arbehbaha/3U_X-Band_CubeSat_Reflectarray_Thesis/Chamber_Code/Media/RA+Narda.jpg

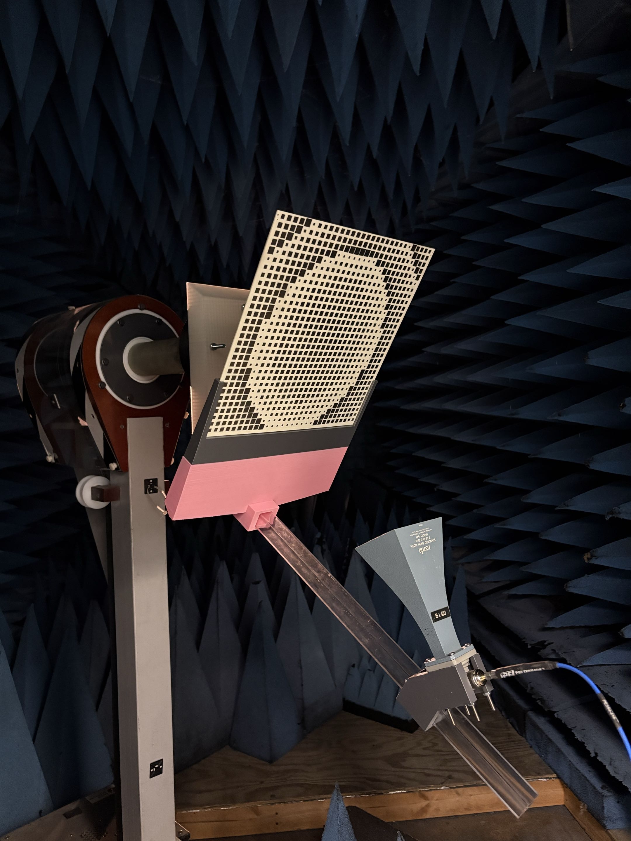
Chamber_Code/Media/RA+Narda.jpg
