arbehbaha/3U_X-Band_CubeSat_Reflectarray_Thesis/Chamber_Code/Narda_Horn_Sweeps_5-3-2026/Narda_641_EH.png

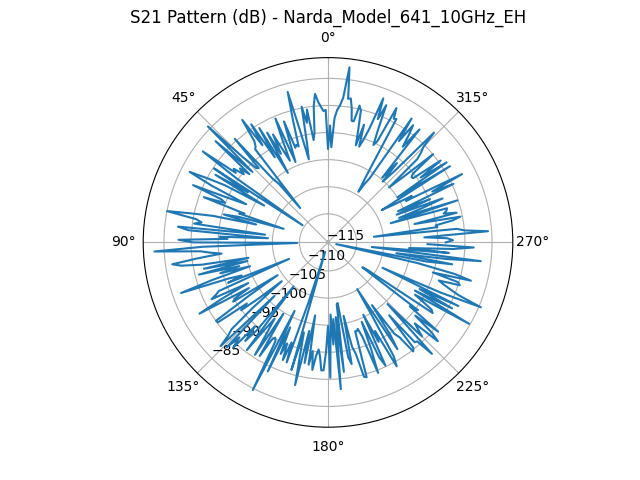
Chamber_Code/Narda_Horn_Sweeps_5-3-2026/Narda_641_EH.png
