arbehbaha/3U_X-Band_CubeSat_Reflectarray_Thesis/Chamber_Code/RA_EH_Sweep_5-3-2026/RA_EE.png

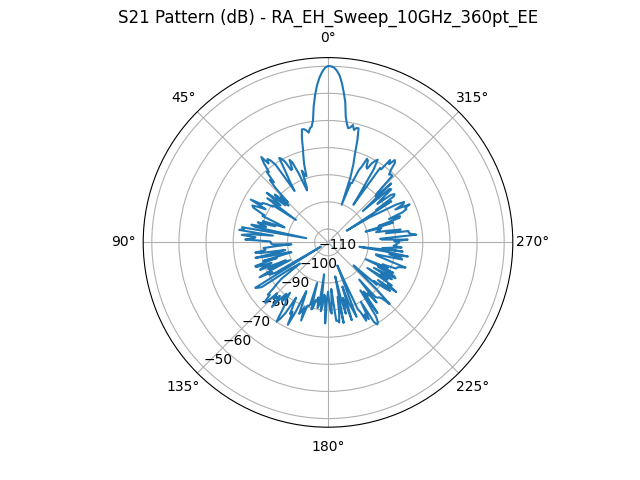
Chamber_Code/RA_EH_Sweep_5-3-2026/RA_EE.png
