arbehbaha/3U_X-Band_CubeSat_Reflectarray_Thesis/Images/chapter-4-figures/horn-mount-cad.png

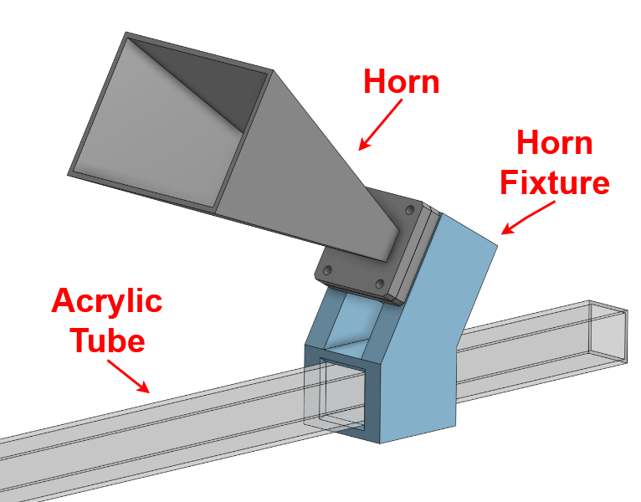
Images/chapter-4-figures/horn-mount-cad.png
