arbehbaha/3U_X-Band_CubeSat_Reflectarray_Thesis/Images/chapter-4-figures/mounted-ra.jpg

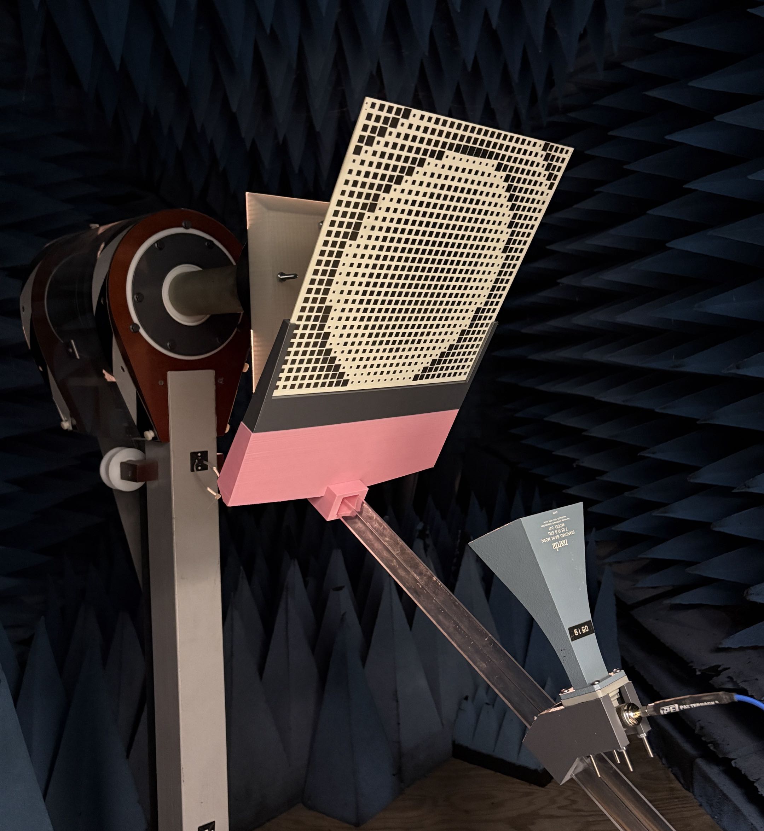
Images/chapter-4-figures/mounted-ra.jpg
