arbehbaha/3U_X-Band_CubeSat_Reflectarray_Thesis/Images/Chapter_1_figures/raincube.png

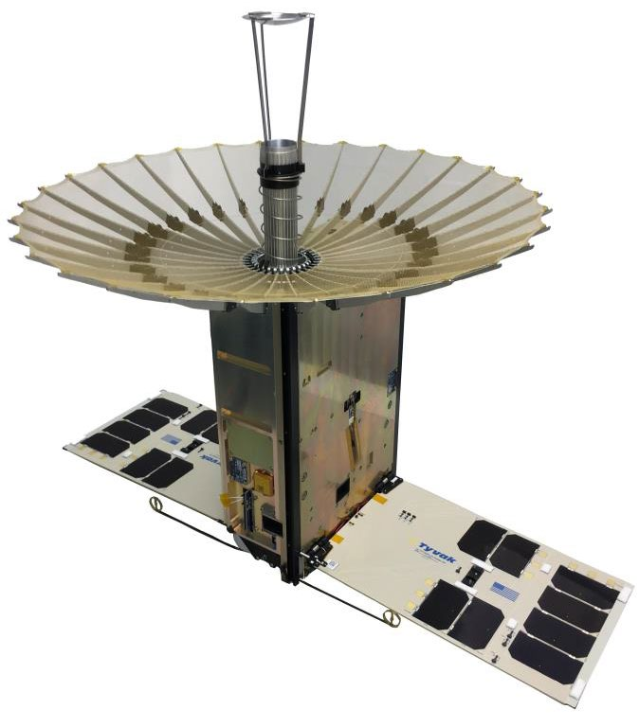
Images/Chapter_1_figures/raincube.png
