arbehbaha/3U_X-Band_CubeSat_Reflectarray_Thesis/Images/chapter_2_figures/Cubesat_group_photo.png

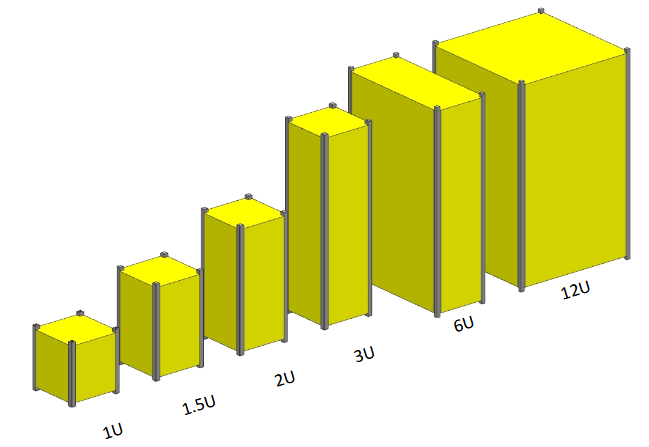
Images/chapter_2_figures/Cubesat_group_photo.png
