arbehbaha/3U_X-Band_CubeSat_Reflectarray_Thesis/Images/chapter_2_figures/frequency_bands_used_in_the_120_cubesat_missions.png

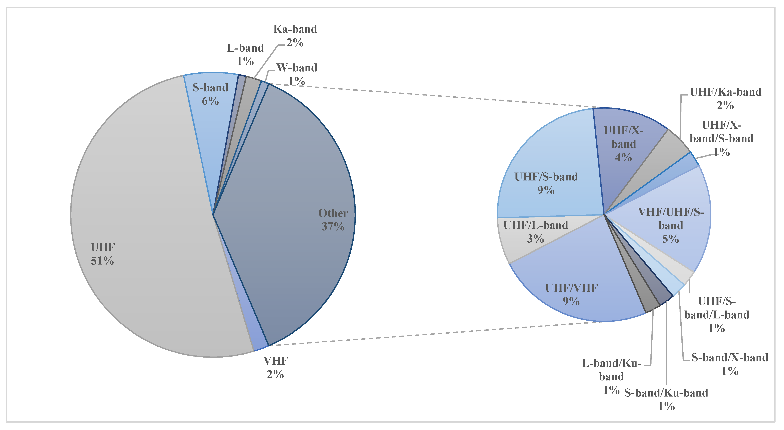
Images/chapter_2_figures/frequency_bands_used_in_the_120_cubesat_missions.png
