arbehbaha/3U_X-Band_CubeSat_Reflectarray_Thesis/Images/chapter_2_figures/generic-reflectarray-geometry.png

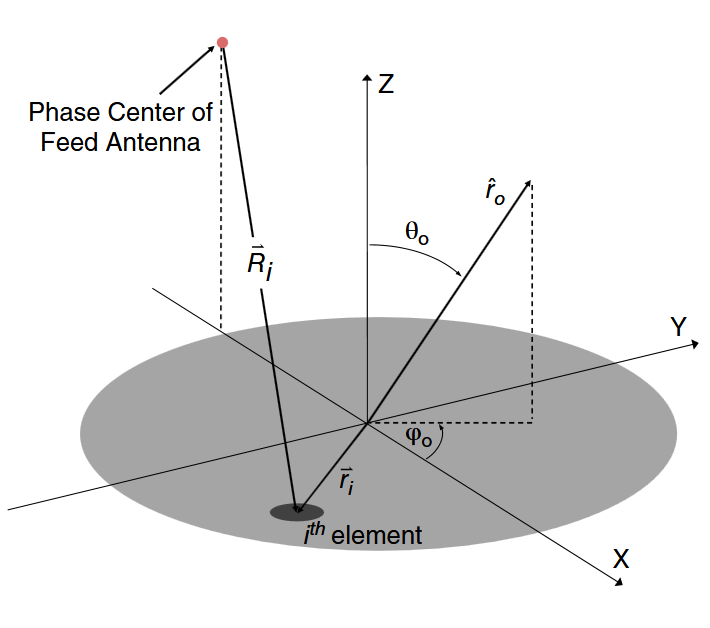
Images/chapter_2_figures/generic-reflectarray-geometry.png
