arbehbaha/3U_X-Band_CubeSat_Reflectarray_Thesis/Images/chapter_2_figures/generic-square-patch.png

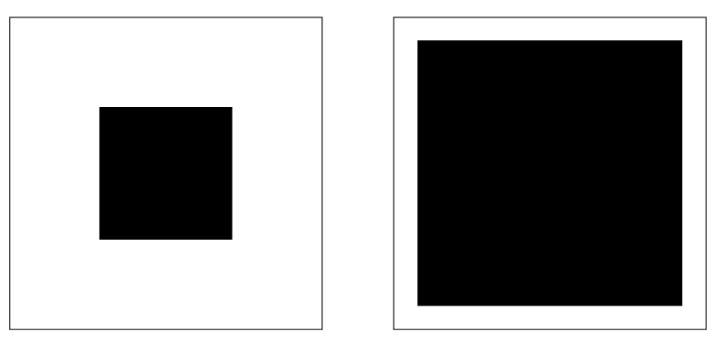
Images/chapter_2_figures/generic-square-patch.png
