arbehbaha/3U_X-Band_CubeSat_Reflectarray_Thesis/Images/chapter_2_figures/isara_antenna_deployment.png

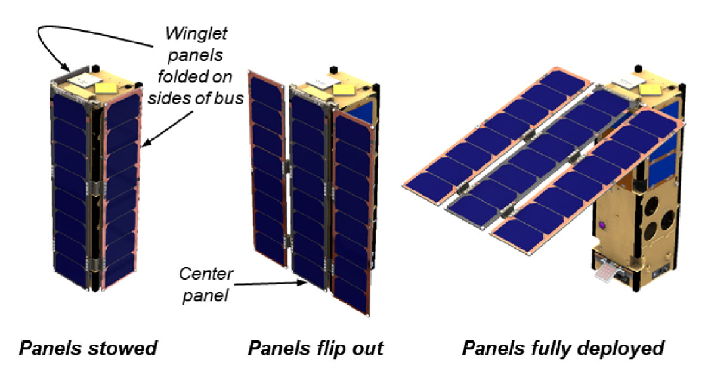
Images/chapter_2_figures/isara_antenna_deployment.png
