arbehbaha/3U_X-Band_CubeSat_Reflectarray_Thesis/Images/chapter_2_figures/isara_cad_model.png

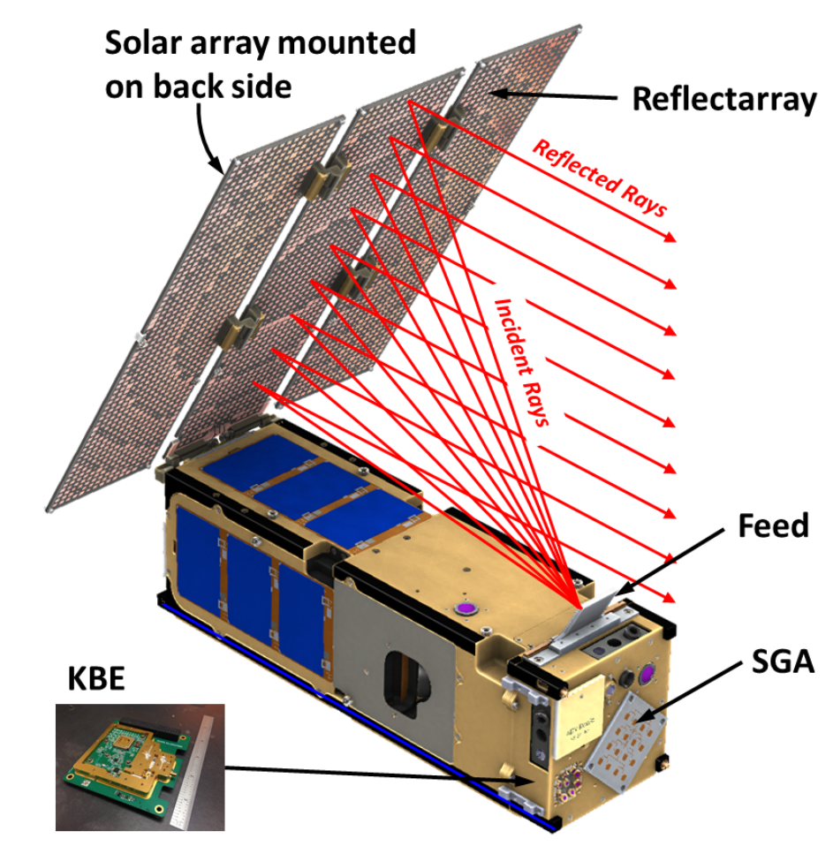
Images/chapter_2_figures/isara_cad_model.png
