arbehbaha/3U_X-Band_CubeSat_Reflectarray_Thesis/Images/chapter_2_figures/Nanosats_years_organisations_2025-12-31_large.png

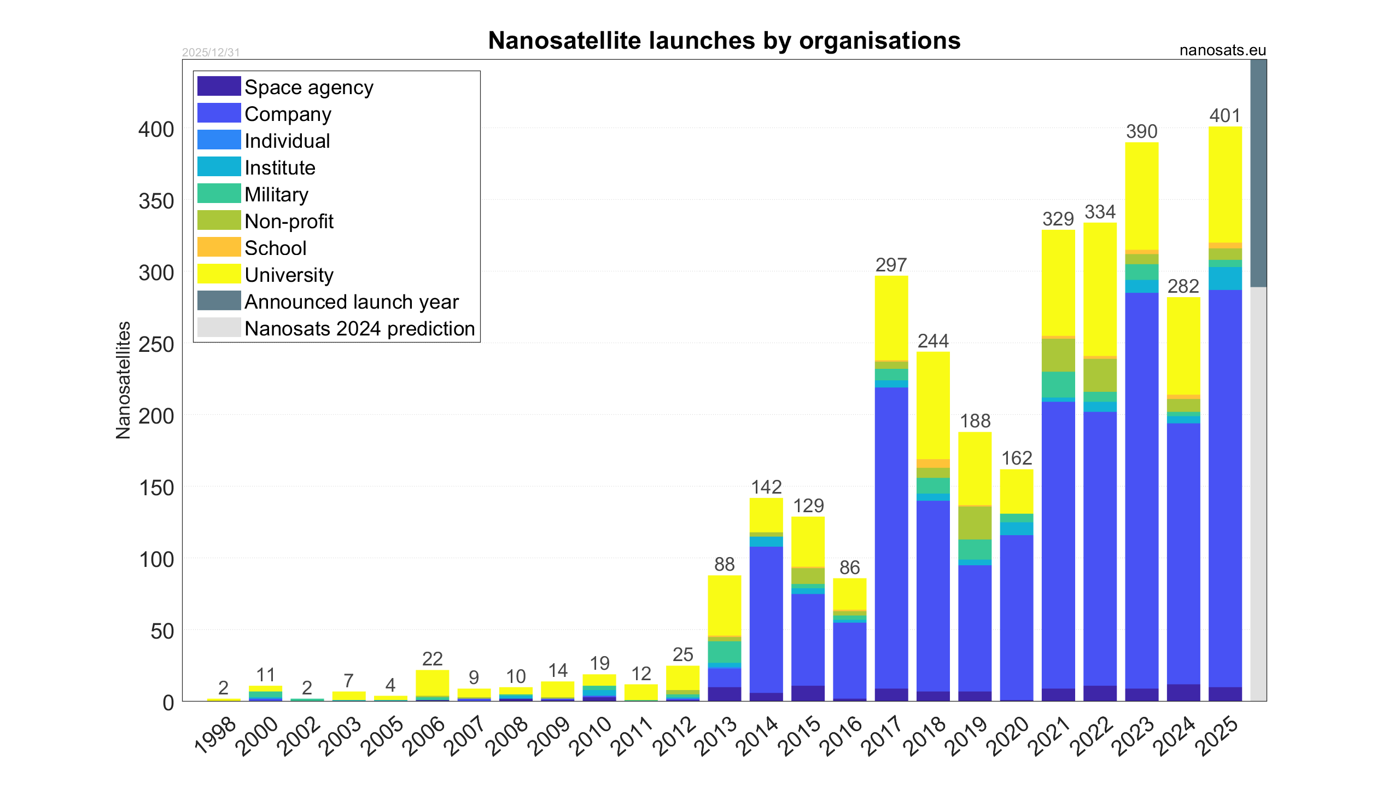
Images/chapter_2_figures/Nanosats_years_organisations_2025-12-31_large.png
