arbehbaha/3U_X-Band_CubeSat_Reflectarray_Thesis/Images/chapter_2_figures/parabolic-reflectarray-analogy.png

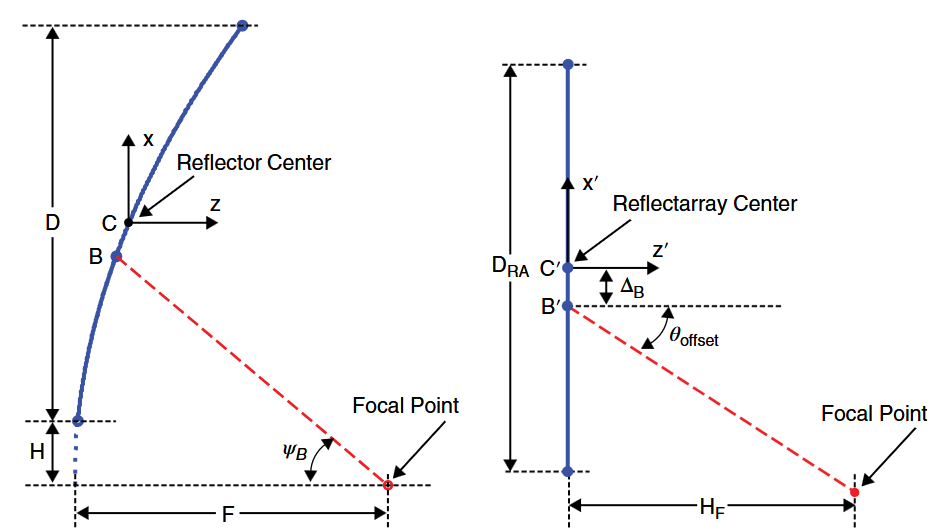
Images/chapter_2_figures/parabolic-reflectarray-analogy.png
