arbehbaha/3U_X-Band_CubeSat_Reflectarray_Thesis/Images/chapter_2_figures/popularity_of_cubesat_mission_types.png

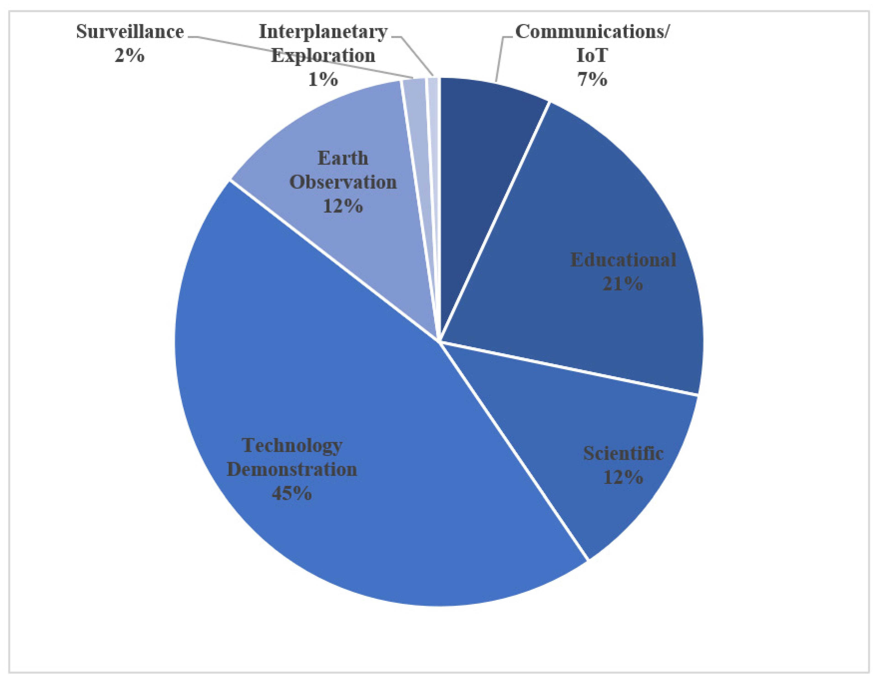
Images/chapter_2_figures/popularity_of_cubesat_mission_types.png
