arbehbaha/3U_X-Band_CubeSat_Reflectarray_Thesis/Images/chapter_2_figures/ra-phase-distributions-b.png

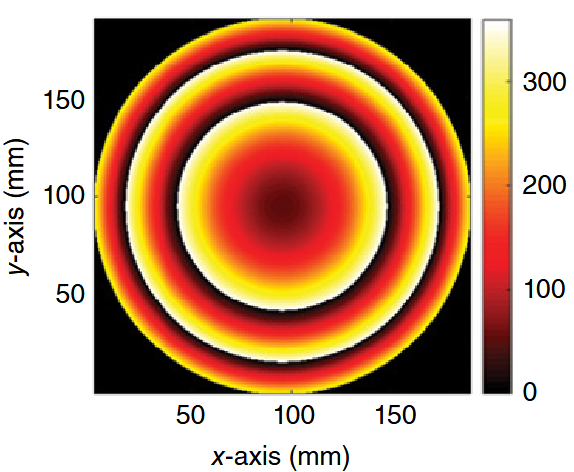
Images/chapter_2_figures/ra-phase-distributions-b.png
