arbehbaha/3U_X-Band_CubeSat_Reflectarray_Thesis/Images/chapter_3_figures/ra-hinge-back.jpg

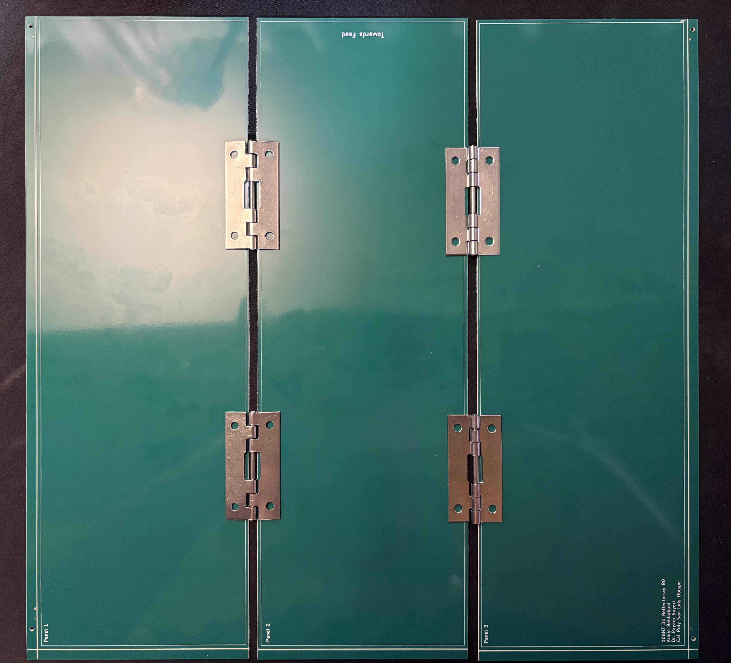
Images/chapter_3_figures/ra-hinge-back.jpg
