arbehbaha/3U_X-Band_CubeSat_Reflectarray_Thesis/Images/chapter_3_figures/ra-layout.png

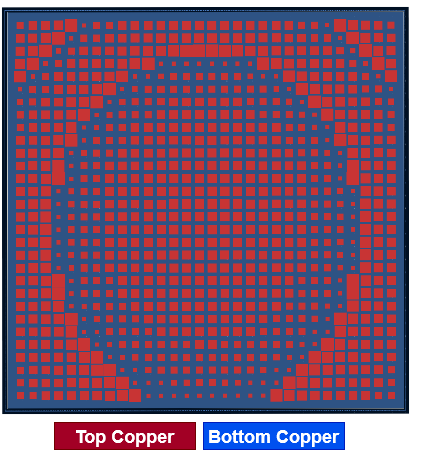
Images/chapter_3_figures/ra-layout.png
