arbehbaha/3U_X-Band_CubeSat_Reflectarray_Thesis/Images/chapter_3_figures/ra-v-score.png

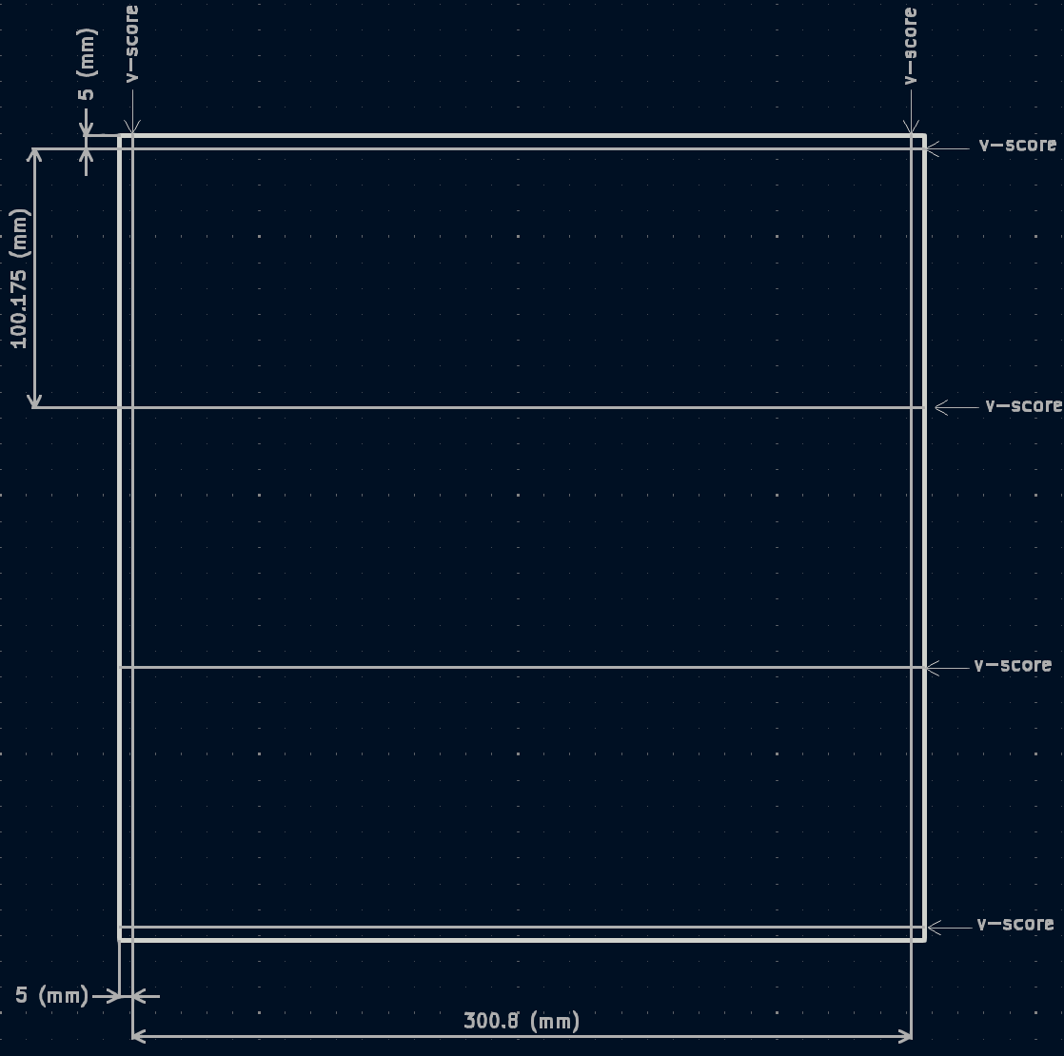
Images/chapter_3_figures/ra-v-score.png
