arbehbaha/3U_X-Band_CubeSat_Reflectarray_Thesis/Images/chapter_3_figures/s-curve-vs-h.png

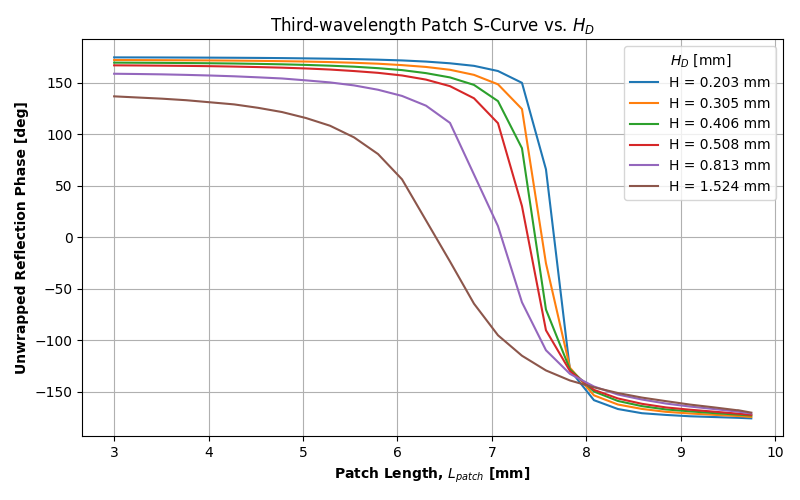
Images/chapter_3_figures/s-curve-vs-h.png
