arbehbaha/3U_X-Band_CubeSat_Reflectarray_Thesis/Images/chapter_3_figures/simulated-patern.png

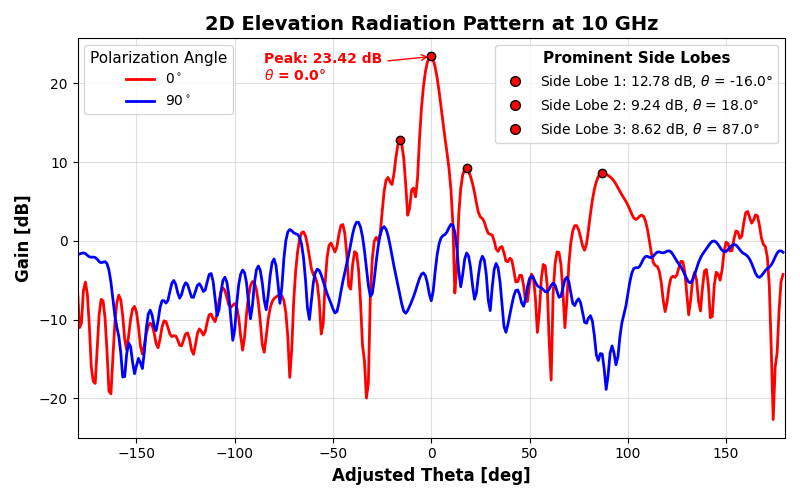
Images/chapter_3_figures/simulated-patern.png
