arbehbaha/3U_X-Band_CubeSat_Reflectarray_Thesis/Images/chapter_3_figures/fabricated-ra-deployment-1.jpg

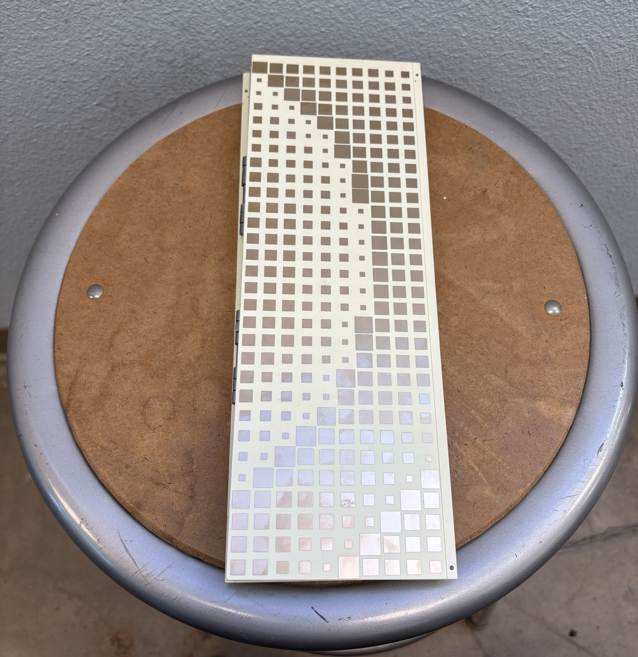
Images/chapter_3_figures/fabricated-ra-deployment-1.jpg
