arbehbaha/3U_X-Band_CubeSat_Reflectarray_Thesis/Images/chapter-4-figures/measured-pattern-hh.png

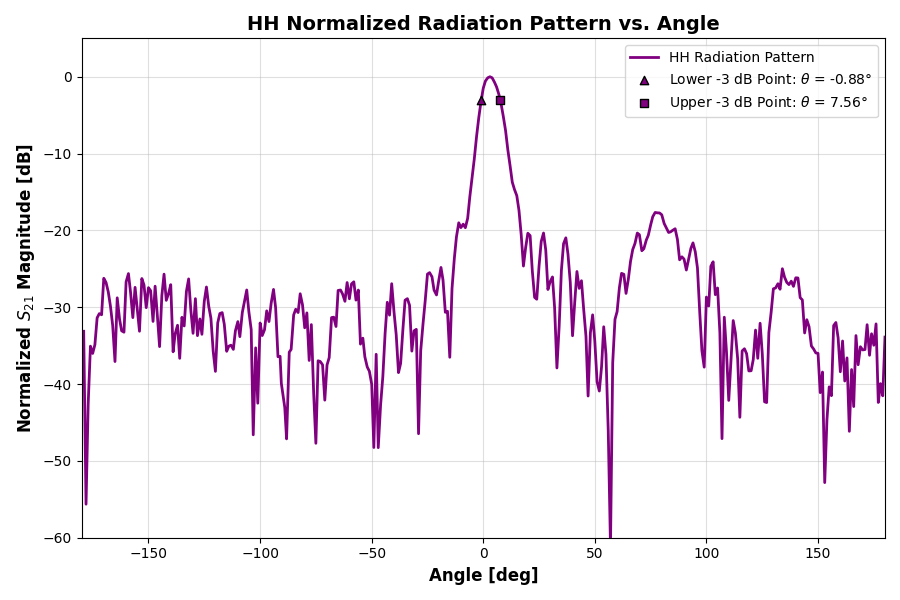
Images/chapter-4-figures/measured-pattern-hh.png
